0ddjob/Osborne_1/EXMON/EXMON_1.jpg

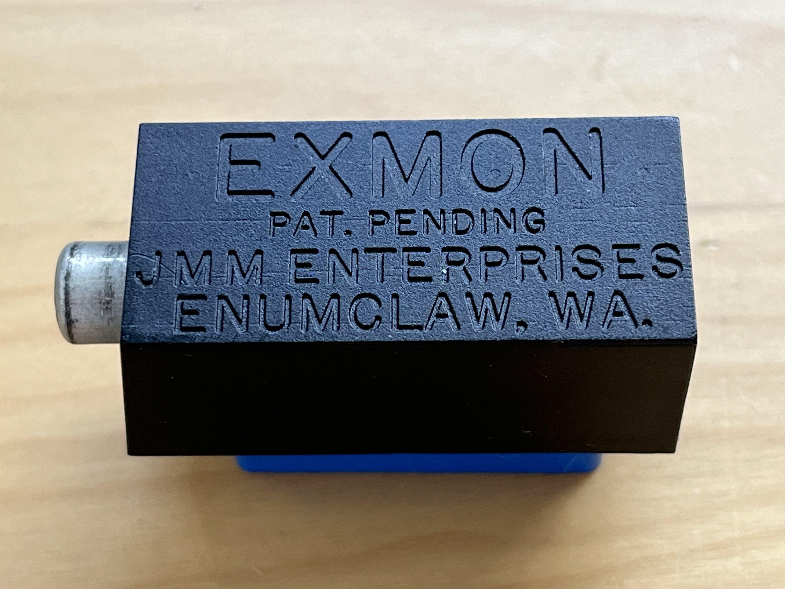
EXMON/EXMON_1.jpg
