0ddjob/Osborne_1/EXMON/EXMON_2.jpg

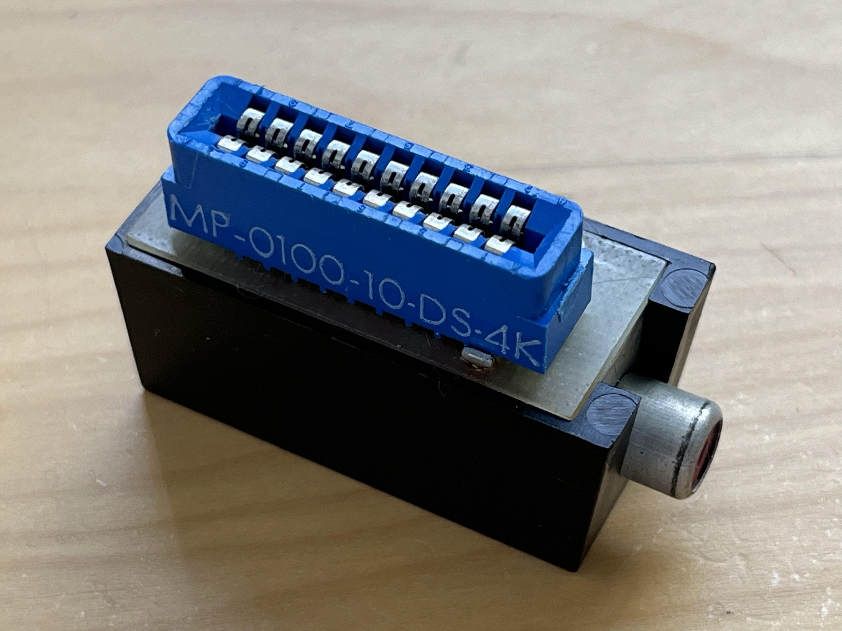
EXMON/EXMON_2.jpg
